wickerwaka/PicoROM/docs/pcb_large.png

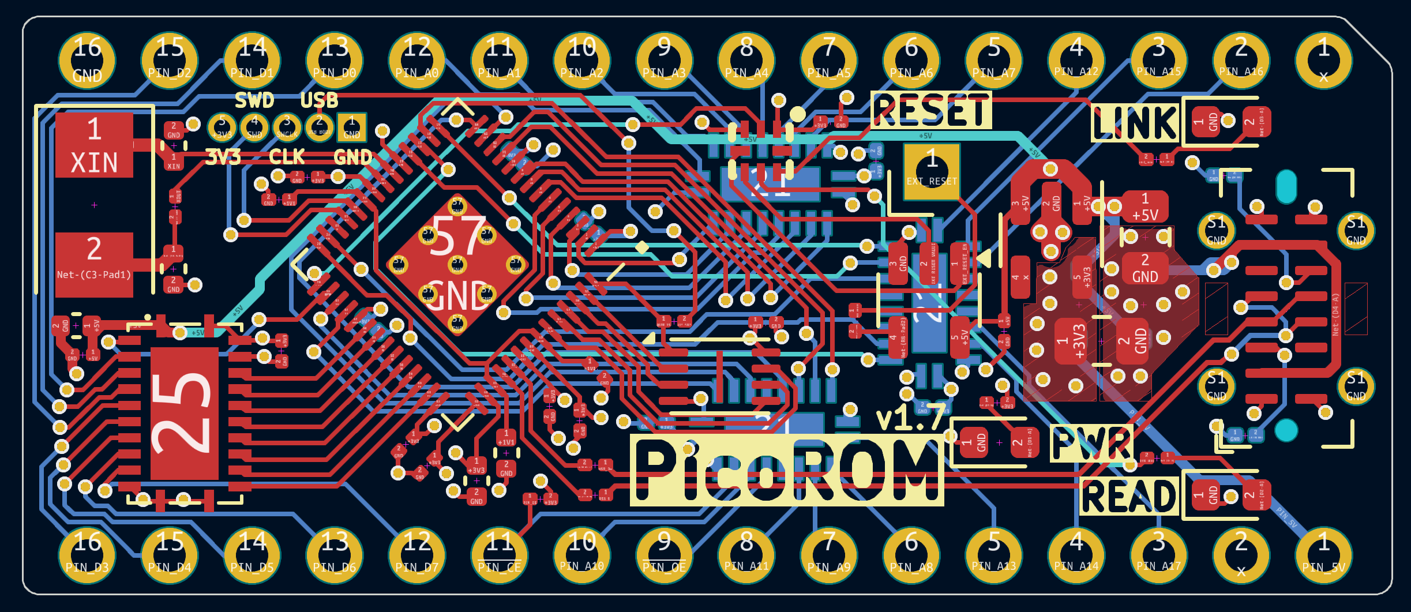
docs/pcb_large.png
